microvax2/H7864-C/Looms/DC Signal Looms.pdf

# DC SIGNAL LOOMS

## Wire:

APAPA22K152 (for 6”) or
APAPA22K305 (for 12”)

Connector Housings: PHDR-08VS

From | To
P1-1 | P2-7
P1-3 | P2-5
P1-2 | P2-8
P1-4 | P2-6

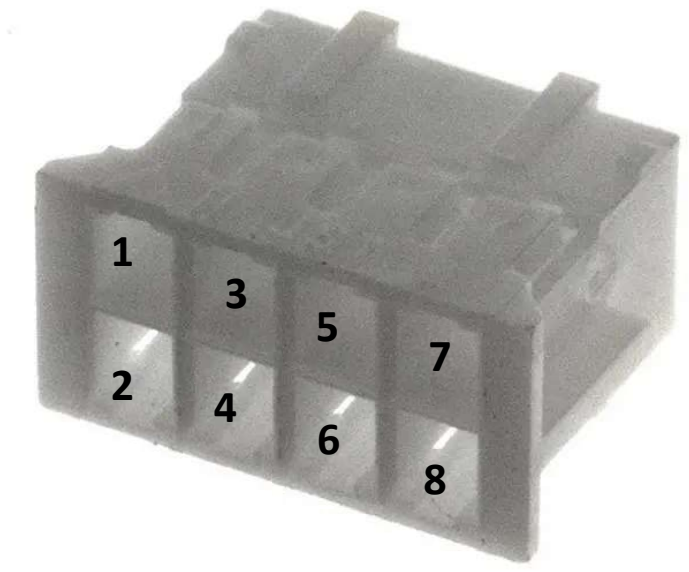
[picture p4: figure]
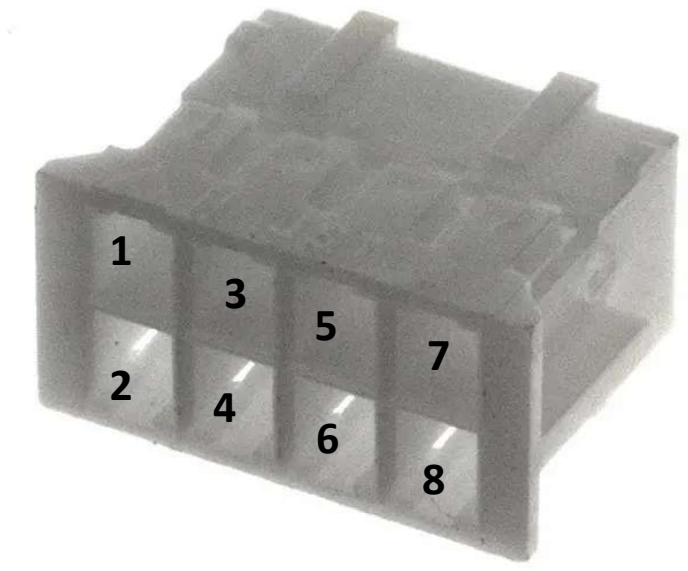
[picture p5: figure]

P1 | P2
