microvax2/H7864-C/Looms/Internal Fan Loom.pdf

### Internal Fan Loom

QUALTEK 07145-12 | - +

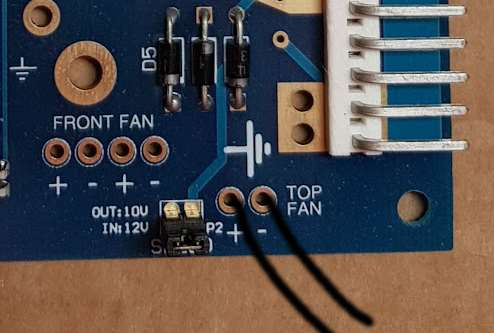
[picture p6: figure]
