microvax2/H7864-C/Looms/J6 Remote On Off Loom.pdf

# J6 - Remote On Off Loom

1-480304-0
Pins: 60619-1

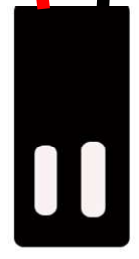
[picture p7: figure]

640250-2
Pins: 640252-2

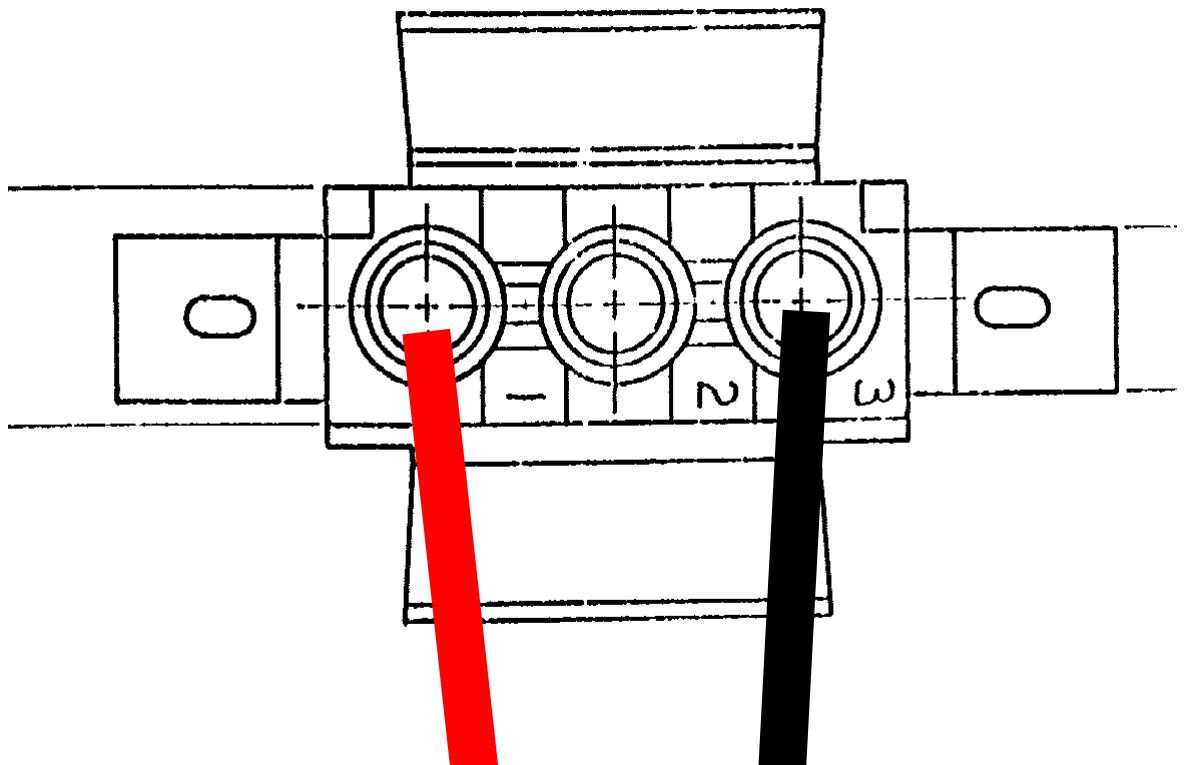
[picture p8: figure]

400mm
