microvax2/H7864-C/Photos and Documents/H7864-C Front Open.JPG

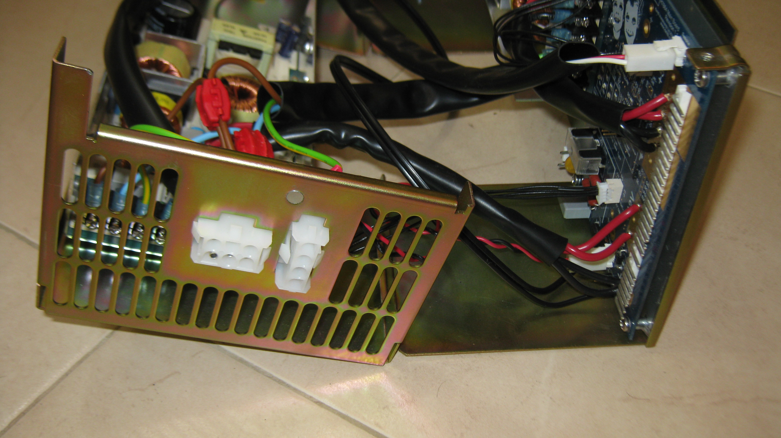
Photos and Documents/H7864-C Front Open.JPG
