microvax2/H7864-C/Photos and Documents/H7864-C Side Open.jpg

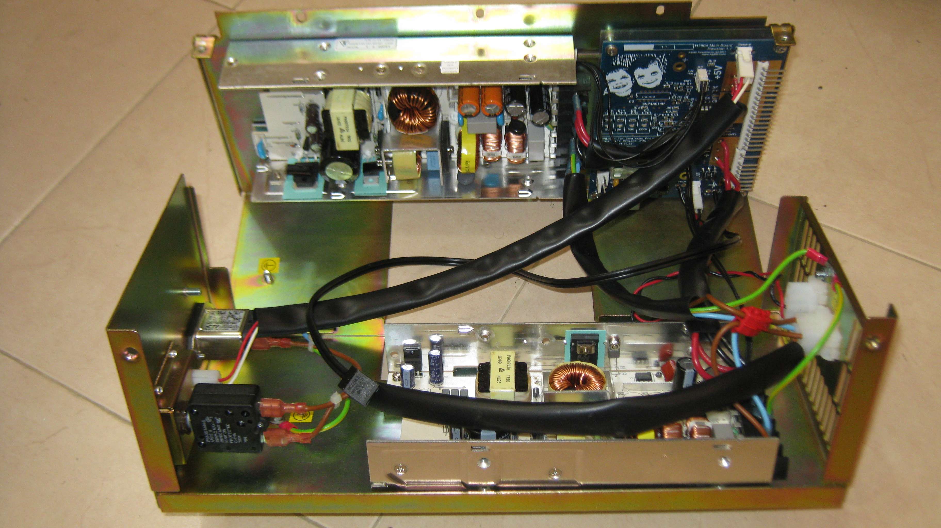
Photos and Documents/H7864-C Side Open.jpg
