microvax2/H7864-C/Photos and Documents/H7864-C vs H7864-B.jpg

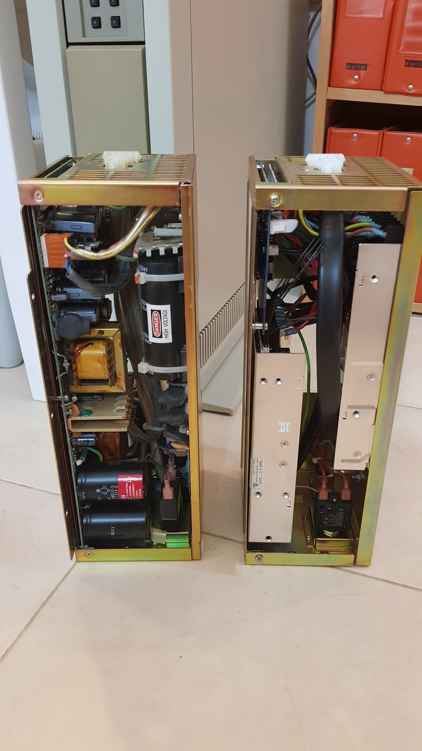
Photos and Documents/H7864-C vs H7864-B.jpg
