microvax2/H7864-C/Photos and Documents/Assembled PCB [1].jpg

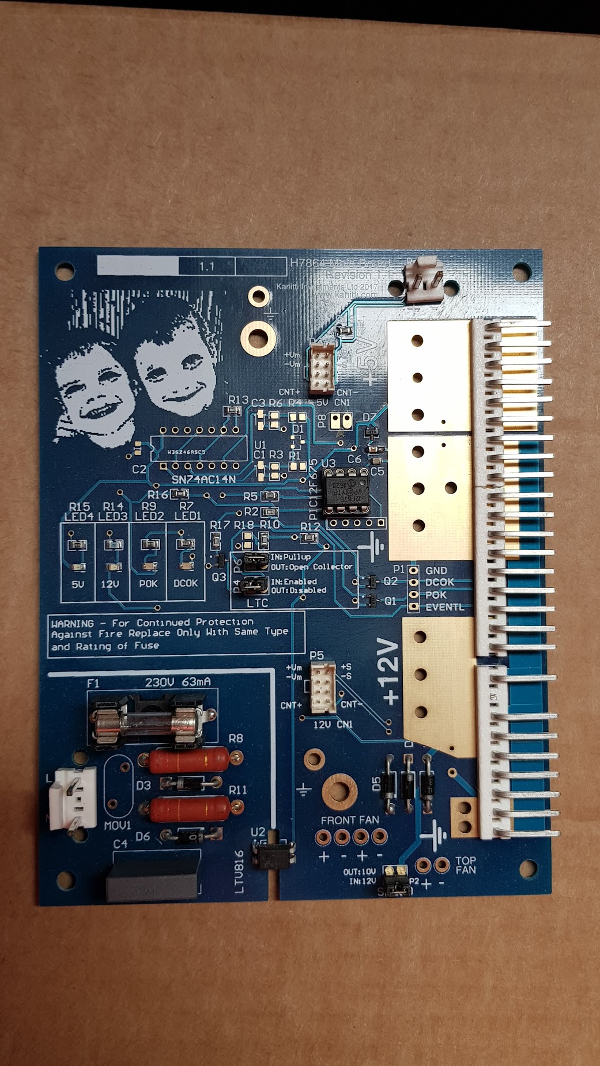
Photos and Documents/Assembled PCB [1].jpg
