microvax2/H7864-C/Software Test Results/50HZ DRY STARTUP 2017-05-10 09-55-45.png

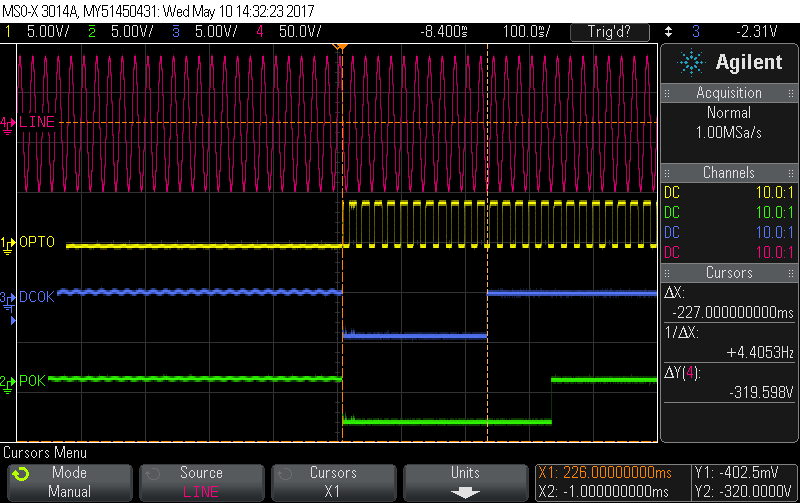
Software Test Results/50HZ DRY STARTUP 2017-05-10 09-55-45.png
