microvax2/H7864-C/Software Test Results/50HZEXP1 2017-05-10 09-37-32.png

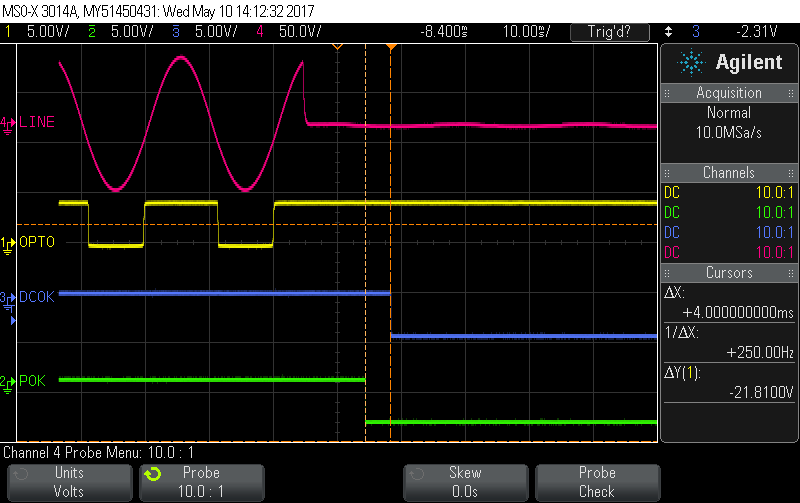
Software Test Results/50HZEXP1 2017-05-10 09-37-32.png
