microvax2/H7864-C/Software Test Results/50HZEXP2 2017-05-10 09-38-30.png

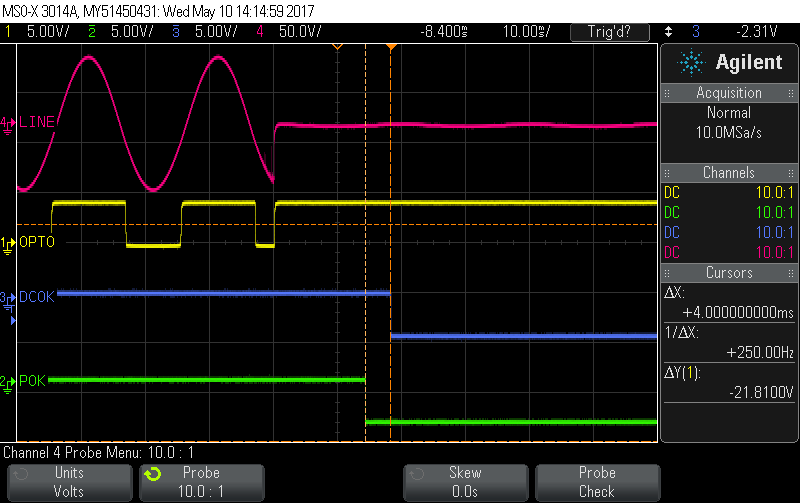
Software Test Results/50HZEXP2 2017-05-10 09-38-30.png
