microvax2/H7864-C/Software Test Results/50HZEXP3 2017-05-10 09-39-35.png

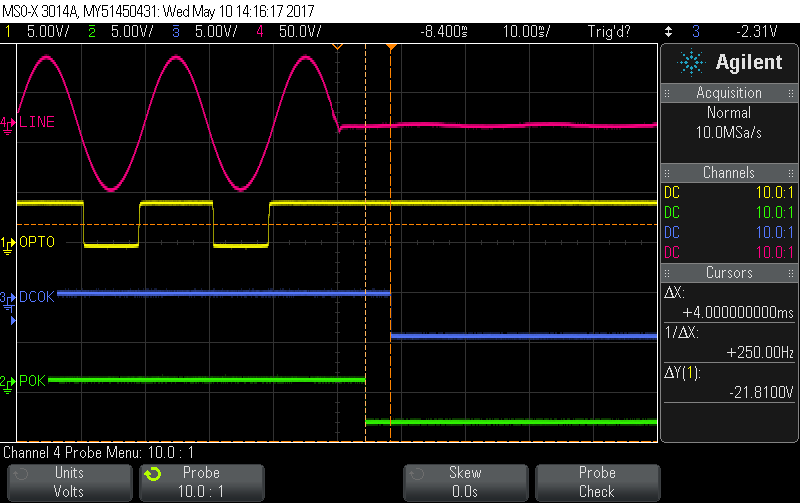
Software Test Results/50HZEXP3 2017-05-10 09-39-35.png
