microvax2/H7864-C/Software Test Results/60HZ DRY STARTUP 2017-05-10 09-54-13.png

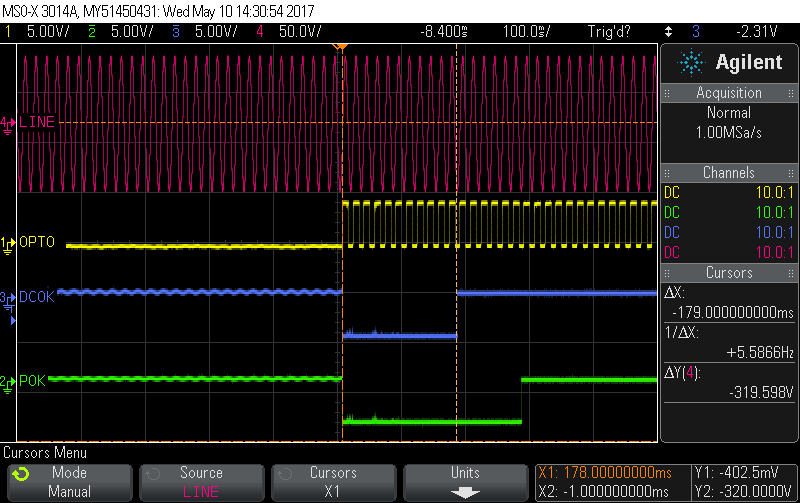
Software Test Results/60HZ DRY STARTUP 2017-05-10 09-54-13.png
