microvax2/H7864-C/Software Test Results/60HZ STARTUP 2017-05-10 09-52-44.png

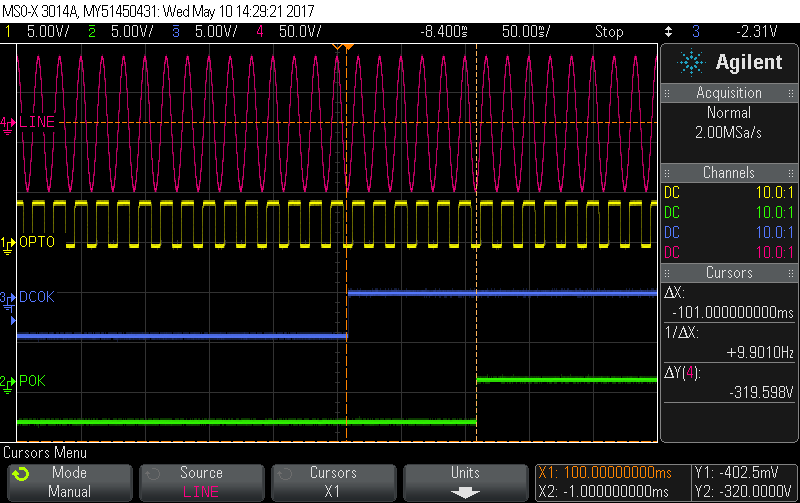
Software Test Results/60HZ STARTUP 2017-05-10 09-52-44.png
