microvax2/H7864-C/Software Test Results/60HZEXP1 2017-05-10 09-48-09.png

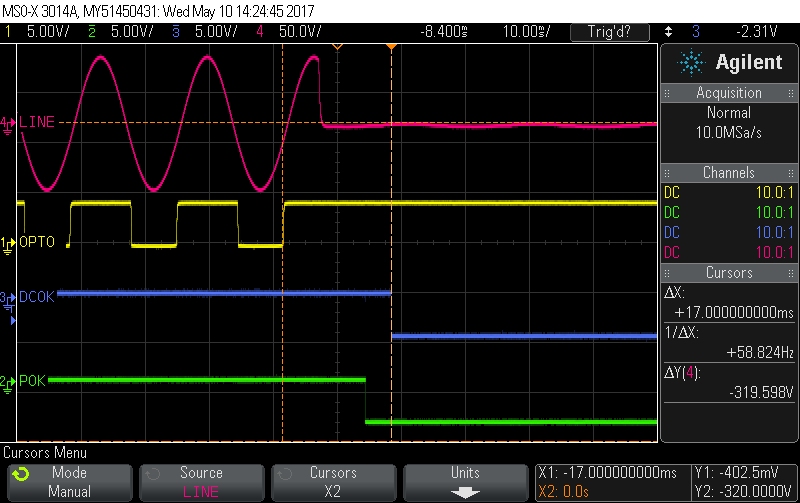
Software Test Results/60HZEXP1 2017-05-10 09-48-09.png
