microvax2/H7864-C/Software Test Results/60HZEXP2 2017-05-10 09-49-37.png

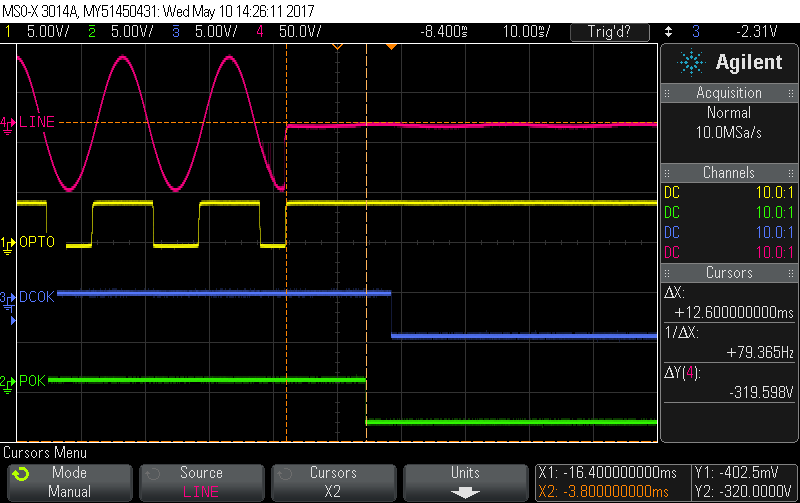
Software Test Results/60HZEXP2 2017-05-10 09-49-37.png
