microvax2/H7864-C/Software Test Results/60HZEXP3 2017-05-10 09-50-55.png

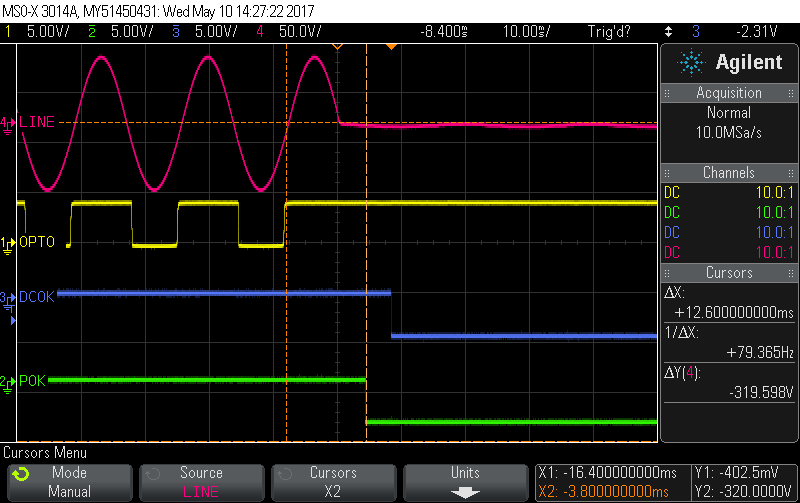
Software Test Results/60HZEXP3 2017-05-10 09-50-55.png
